dTOOR/TheCyrclePhone4G/Media/Glam Shot - Woman Rainbow Plaid - Cropped.jpg

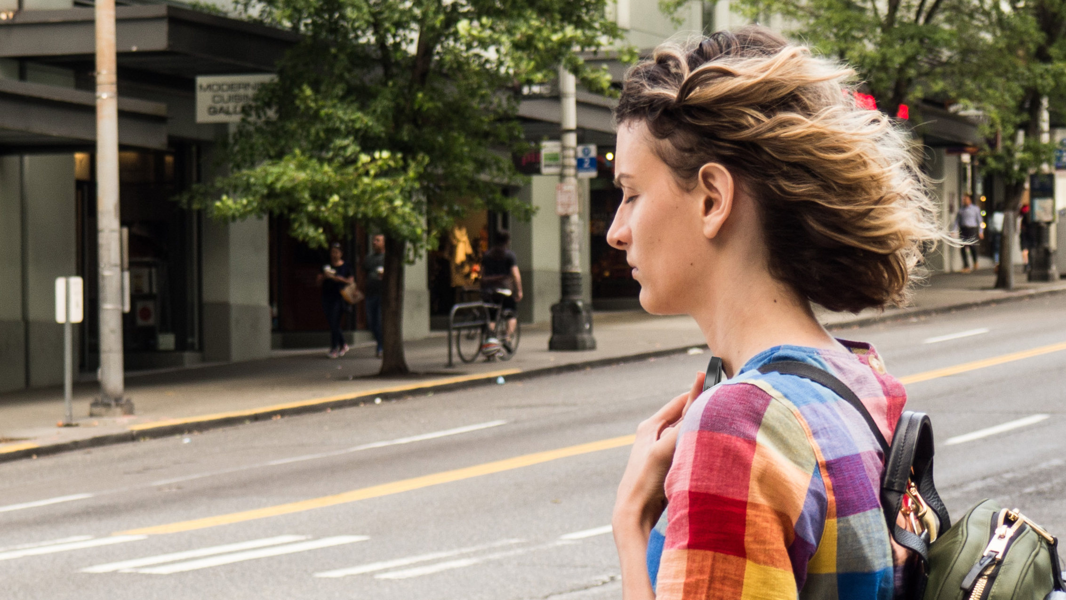
Media/Glam Shot - Woman Rainbow Plaid - Cropped.jpg
