dTOOR/TheCyrclePhone4G/Media/Glam Shots - Business Man - Cropped.jpg

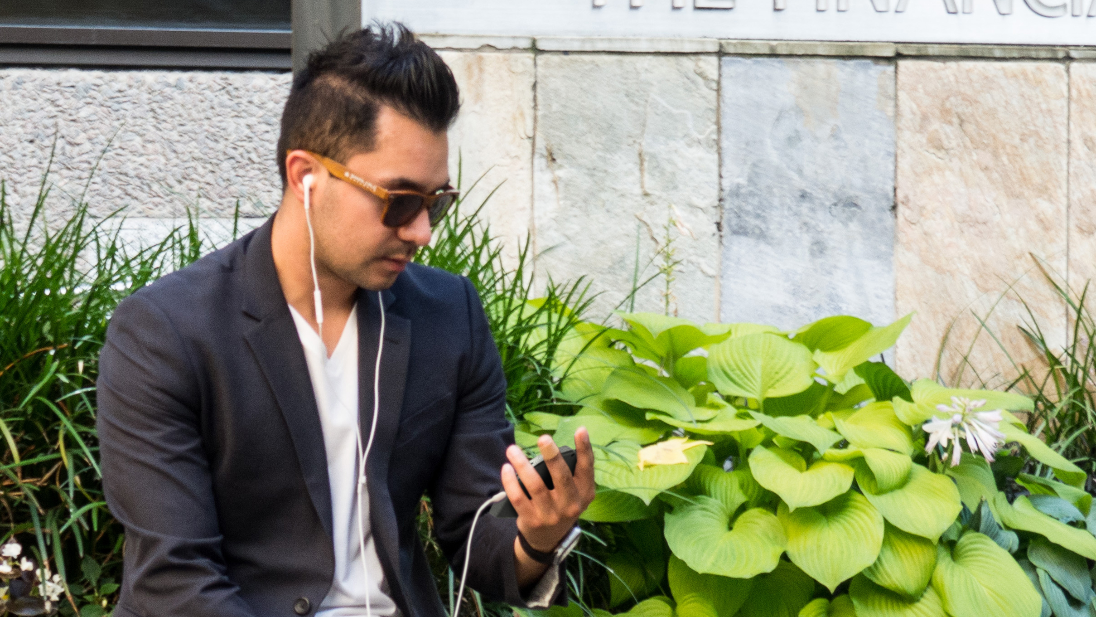
Media/Glam Shots - Business Man - Cropped.jpg
