dTOOR/TheCyrclePhone4G/Media/IMG_6161.jpg

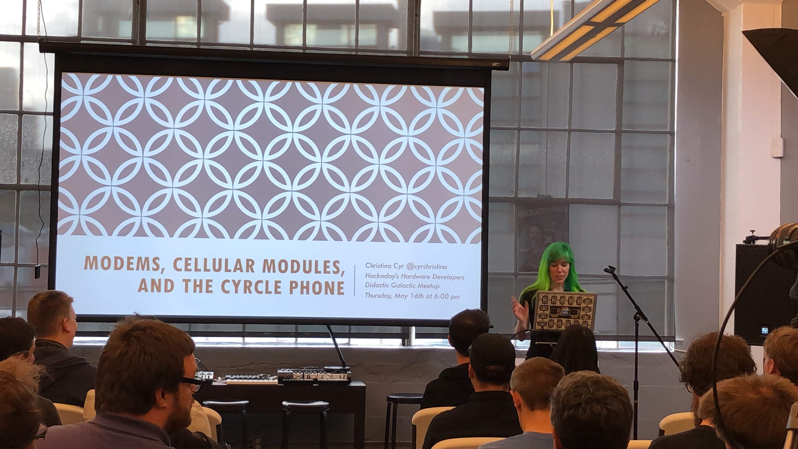
Media/IMG_6161.jpg
