dTOOR/TheCyrclePhone4G/Media/IMG_6163.jpg

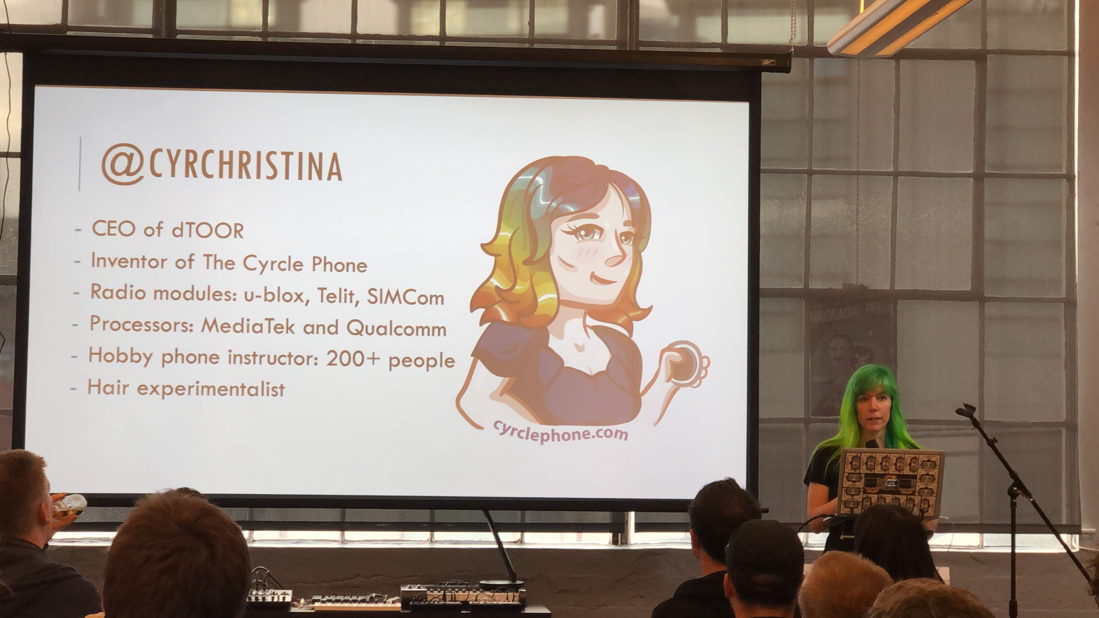
Media/IMG_6163.jpg
