dTOOR/TheCyrclePhone4G/Media/IMG_6170.jpg

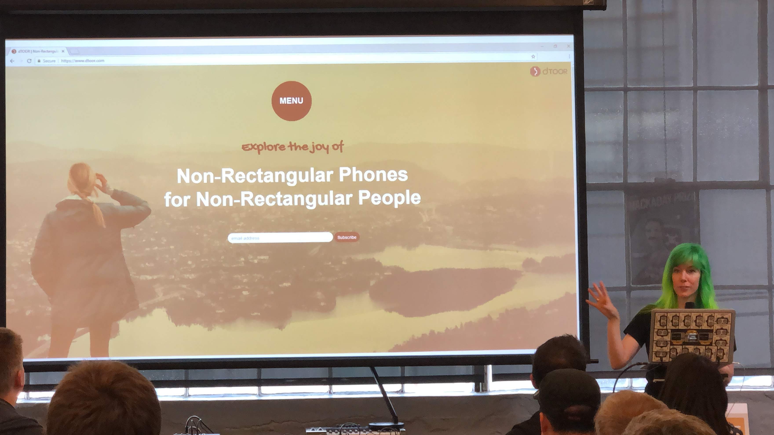
Media/IMG_6170.jpg
