dTOOR/TheCyrclePhone4G/Media/IMG_6492.jpg

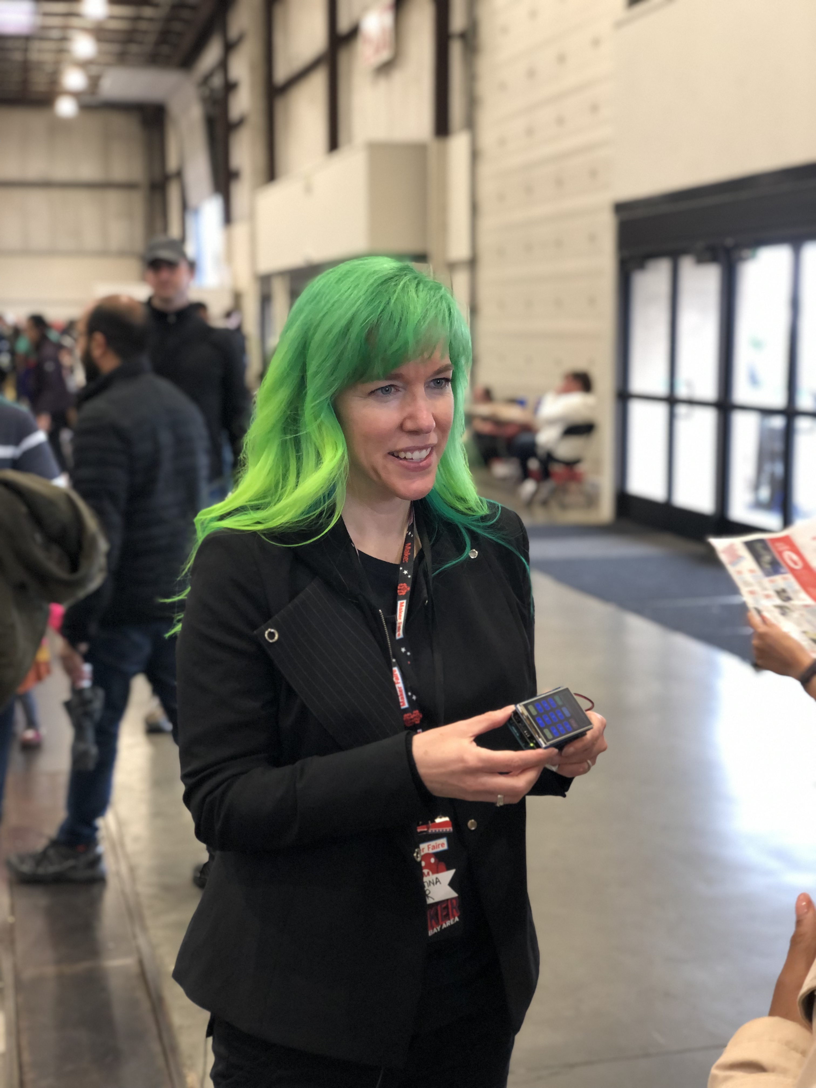
Media/IMG_6492.jpg
