dTOOR/TheCyrclePhone4G/Media/IMG_6493.jpg

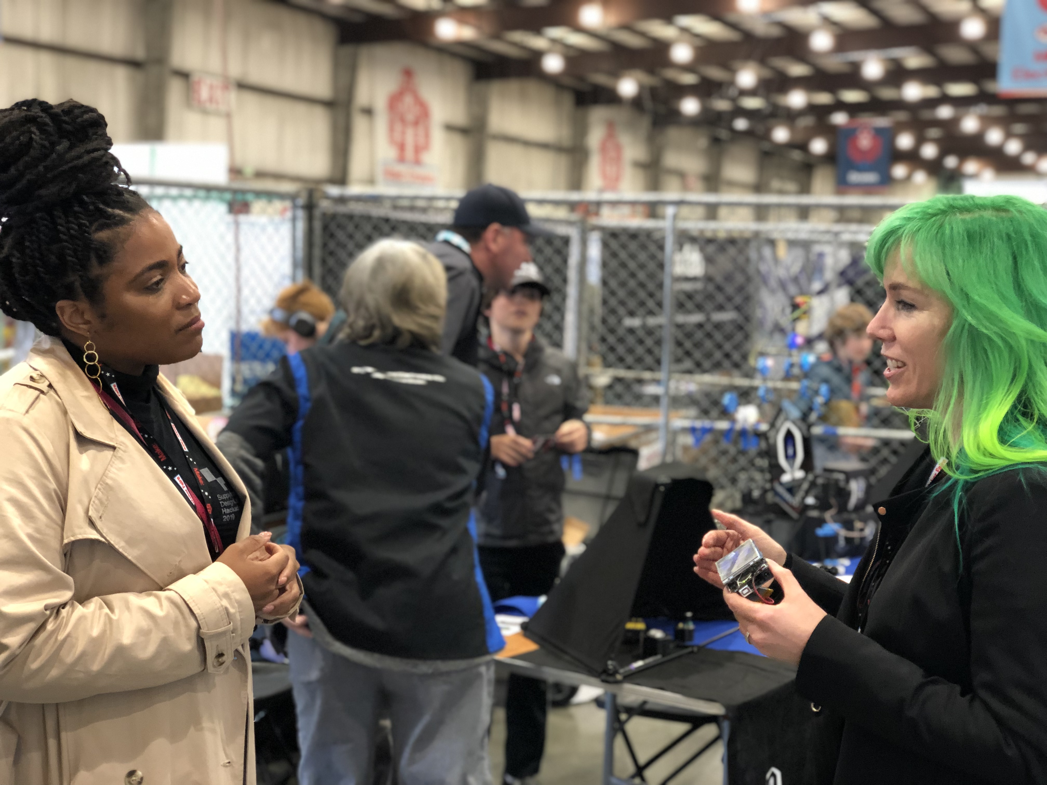
Media/IMG_6493.jpg
