dTOOR/TheCyrclePhone4G/Media/MFBA19_IMG_6429b.jpg

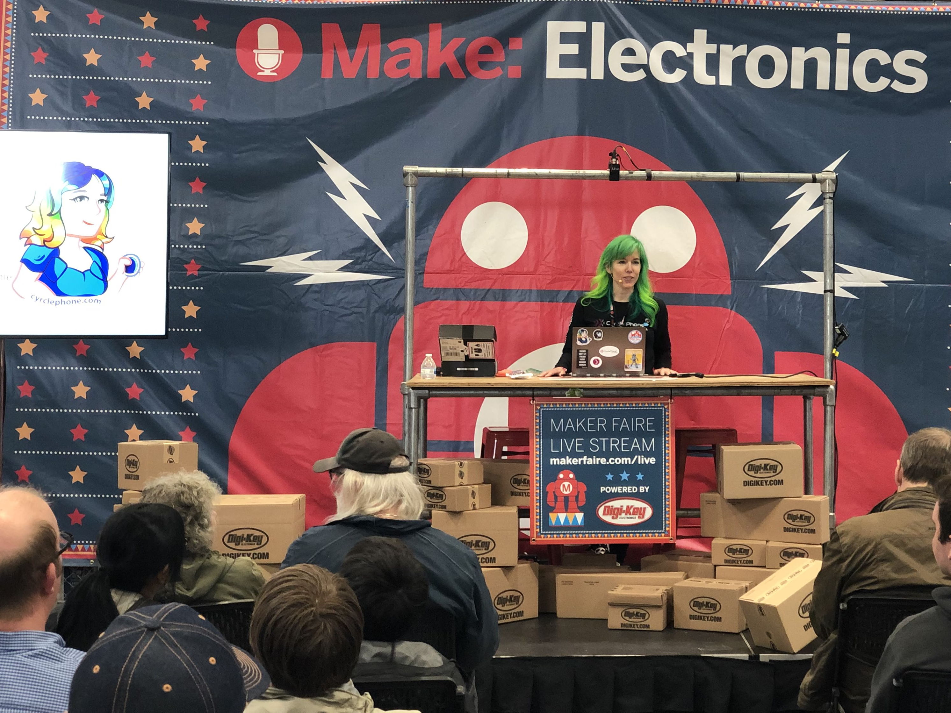
Media/MFBA19_IMG_6429b.jpg
